diogomrts/vocetempo/enclosure/previews/panda_paws.png

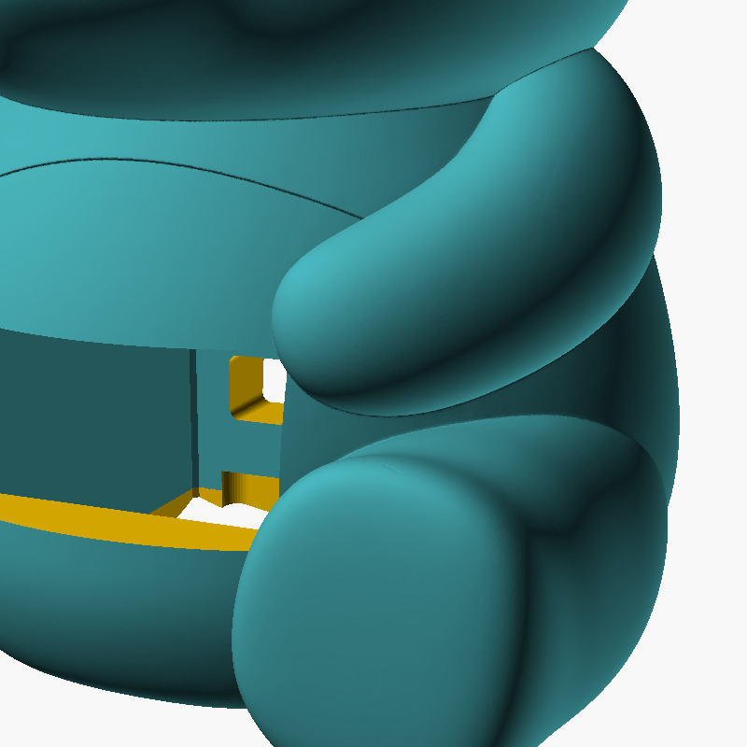
enclosure/previews/panda_paws.png
