diogomrts/vocetempo/enclosure/previews/cage_back.png

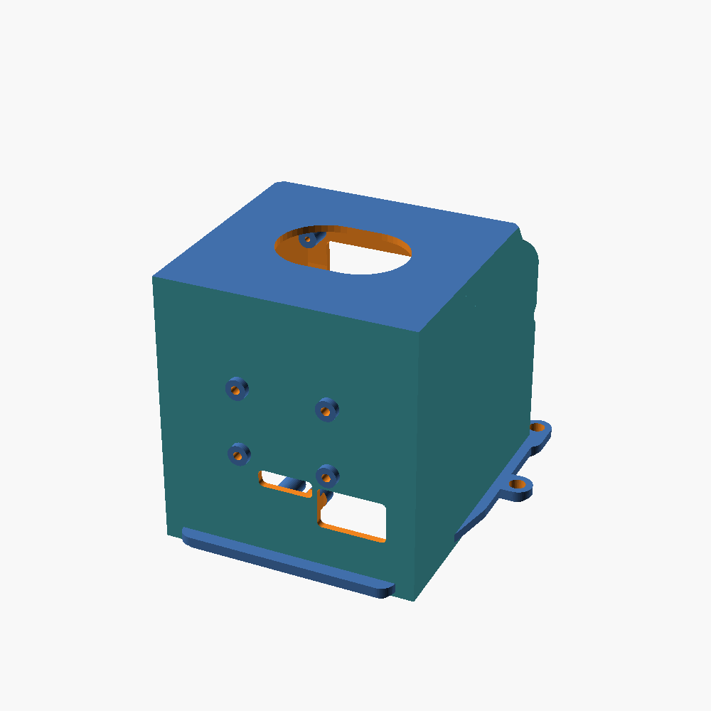
enclosure/previews/cage_back.png
