diogomrts/vocetempo/enclosure/previews/cage_cutouts_comparison_v8.png

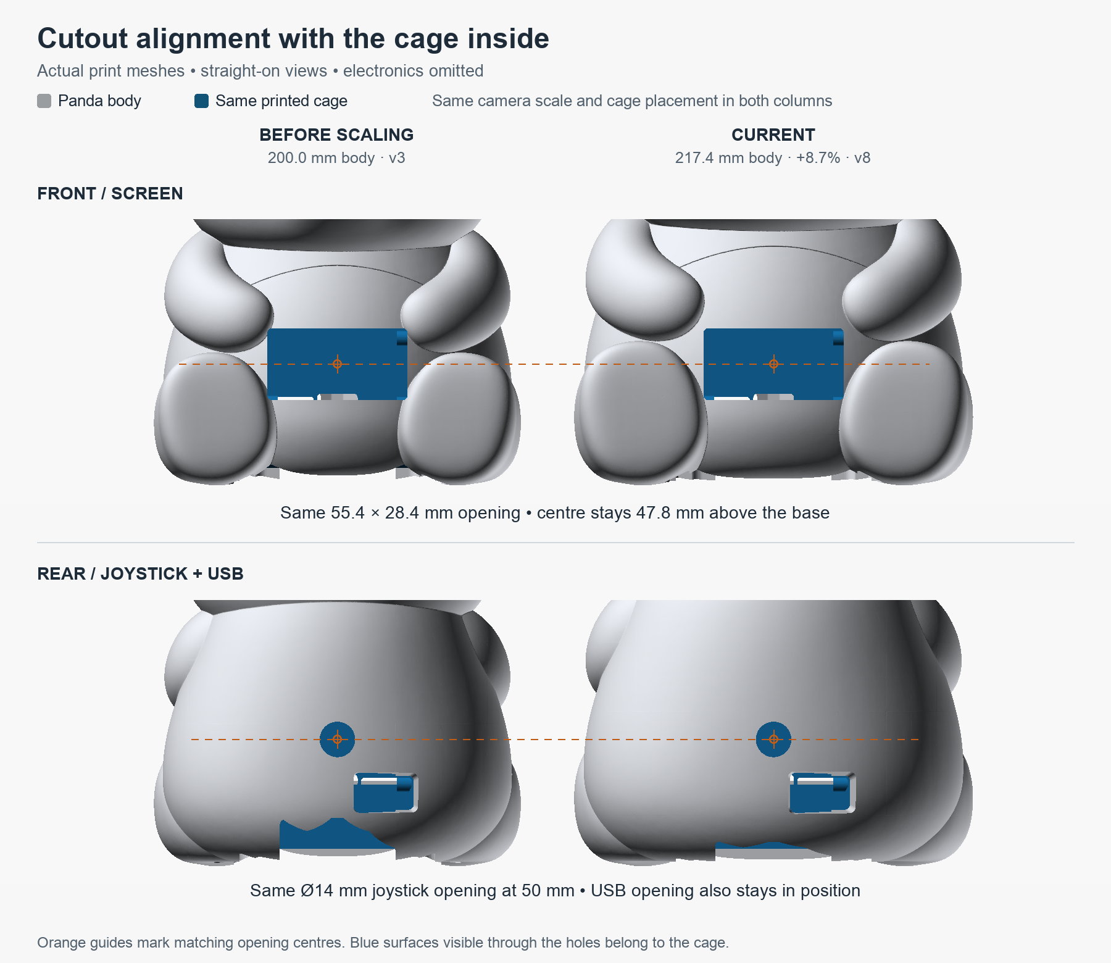
enclosure/previews/cage_cutouts_comparison_v8.png
