diogomrts/vocetempo/enclosure/previews/cage_final.png

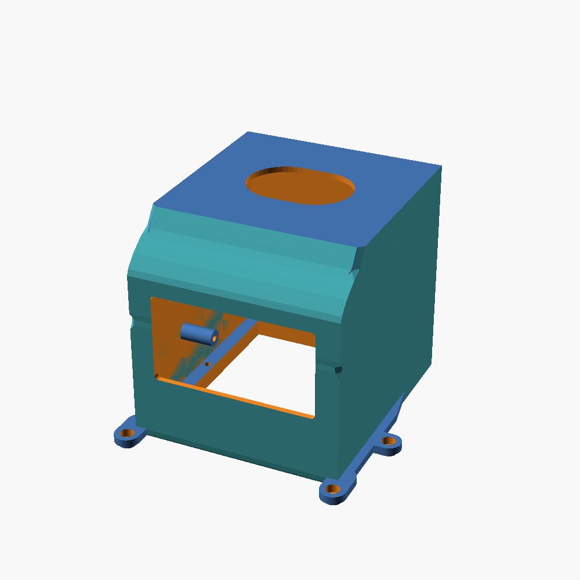
enclosure/previews/cage_final.png
