diogomrts/vocetempo/enclosure/previews/cage_section_comparison_v8.png

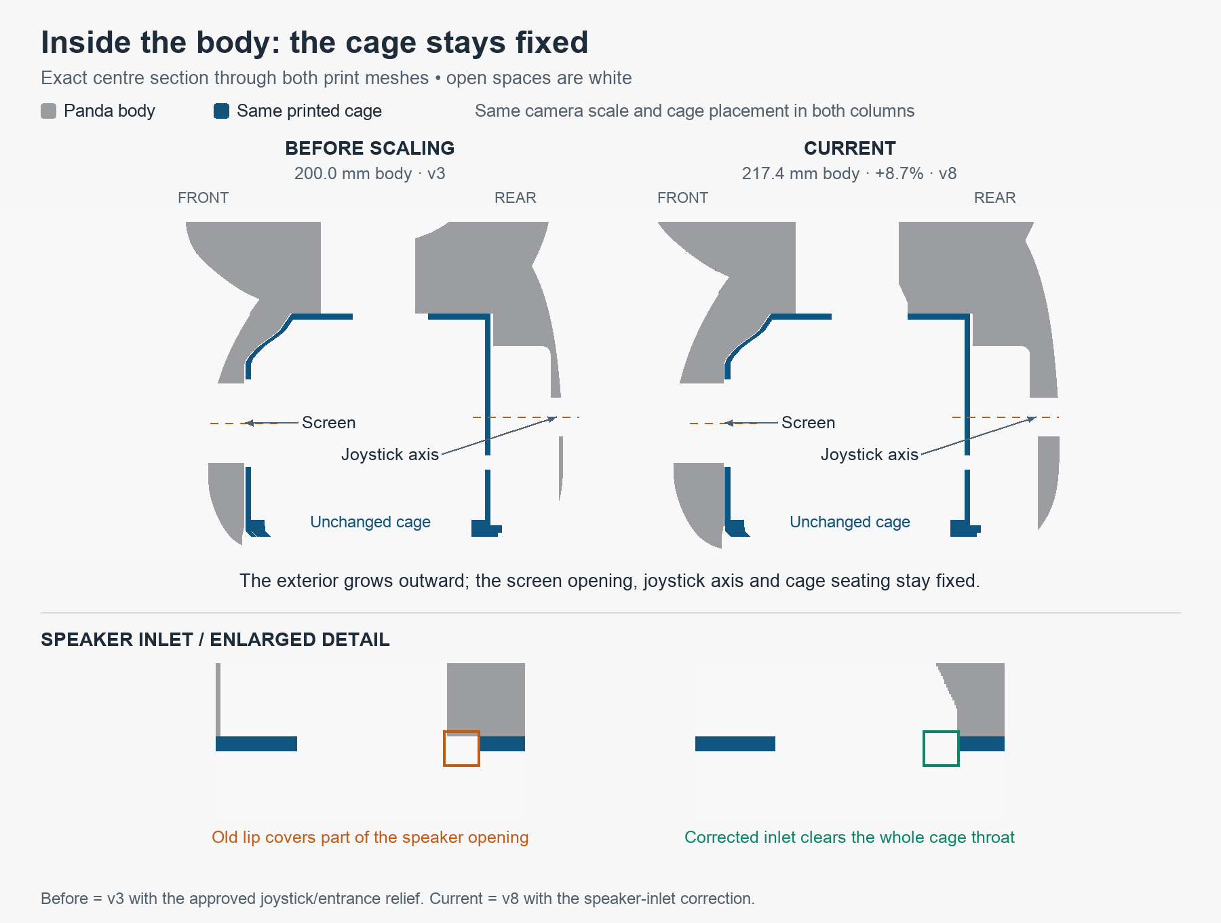
enclosure/previews/cage_section_comparison_v8.png
