diogomrts/vocetempo/enclosure/previews/cover.png

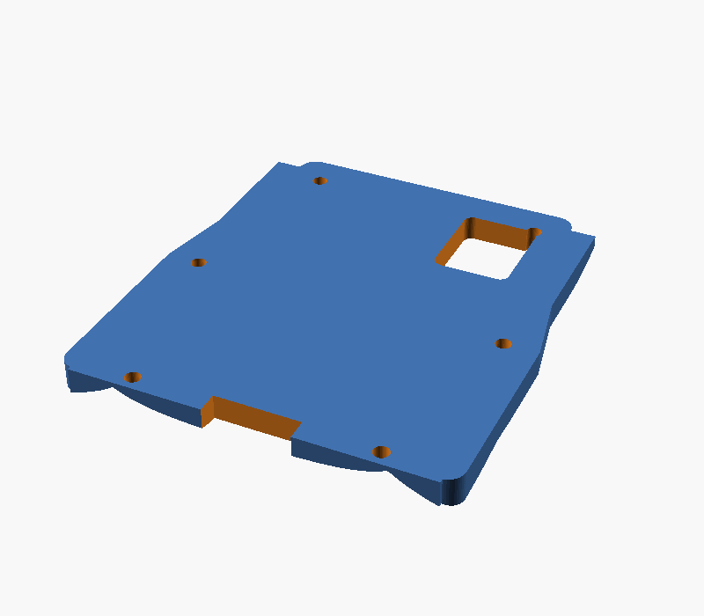
enclosure/previews/cover.png
