diogomrts/vocetempo/enclosure/previews/dfp_bar.png

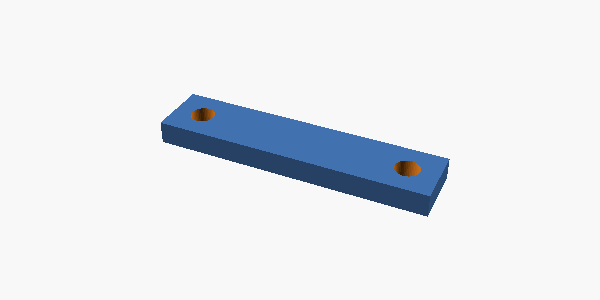
enclosure/previews/dfp_bar.png
