diogomrts/vocetempo/enclosure/previews/entrance_comparison_v3.png

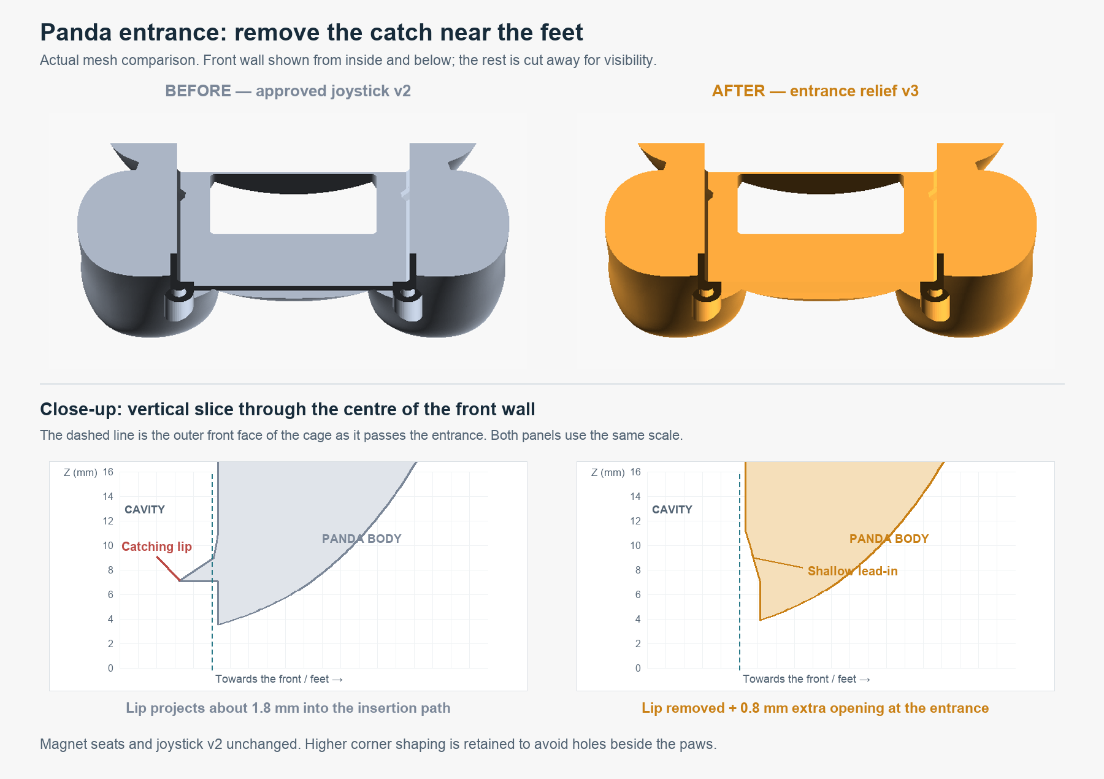
enclosure/previews/entrance_comparison_v3.png
