diogomrts/vocetempo/enclosure/previews/expanded_rump_comparison_v5.png

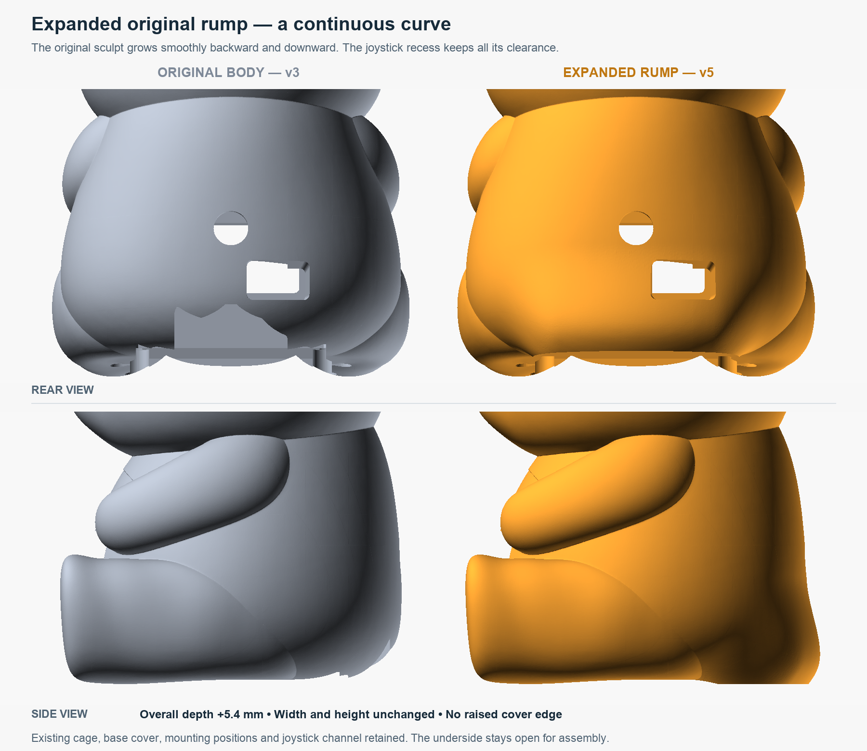
enclosure/previews/expanded_rump_comparison_v5.png
