diogomrts/vocetempo/enclosure/previews/fitcheck.png

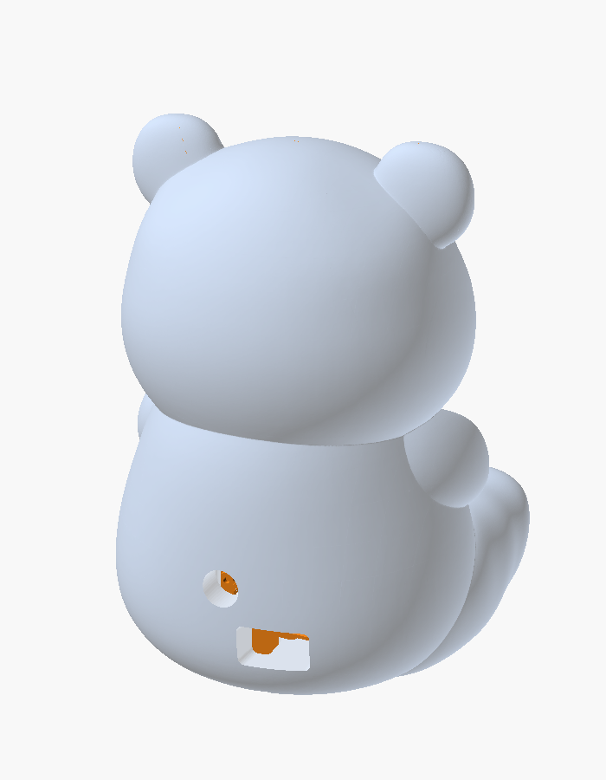
enclosure/previews/fitcheck.png
