diogomrts/vocetempo/enclosure/previews/fitcheck_section.png

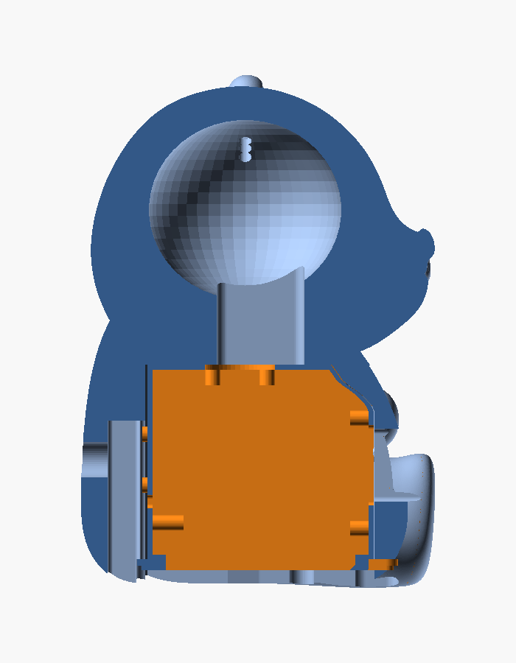
enclosure/previews/fitcheck_section.png
