diogomrts/vocetempo/enclosure/previews/joy_cap.png

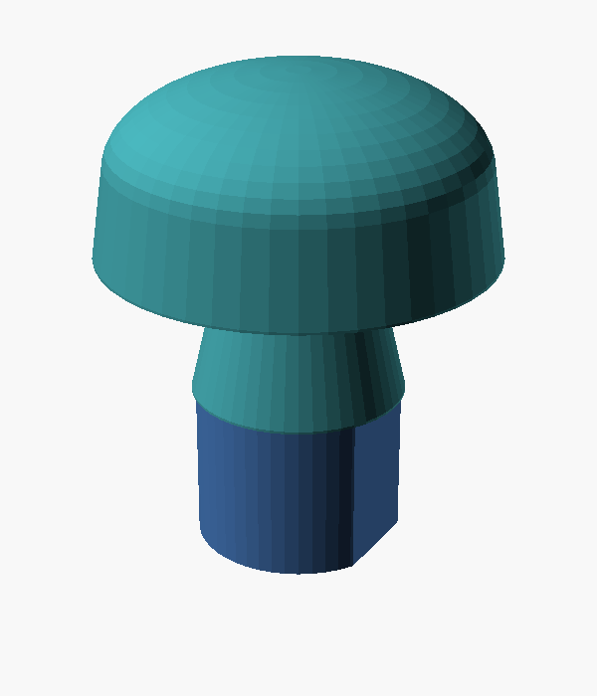
enclosure/previews/joy_cap.png
