diogomrts/vocetempo/enclosure/previews/joystick_bottom_comparison.png

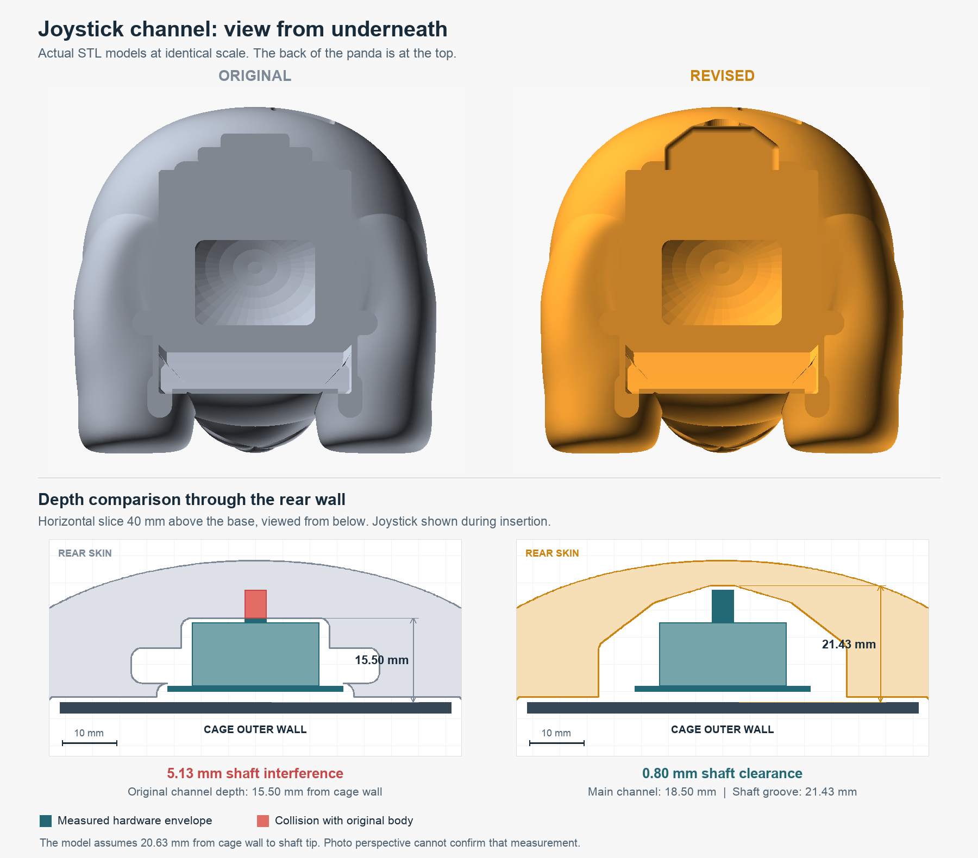
enclosure/previews/joystick_bottom_comparison.png
