diogomrts/vocetempo/enclosure/previews/joystick_bottom_comparison_v2.png

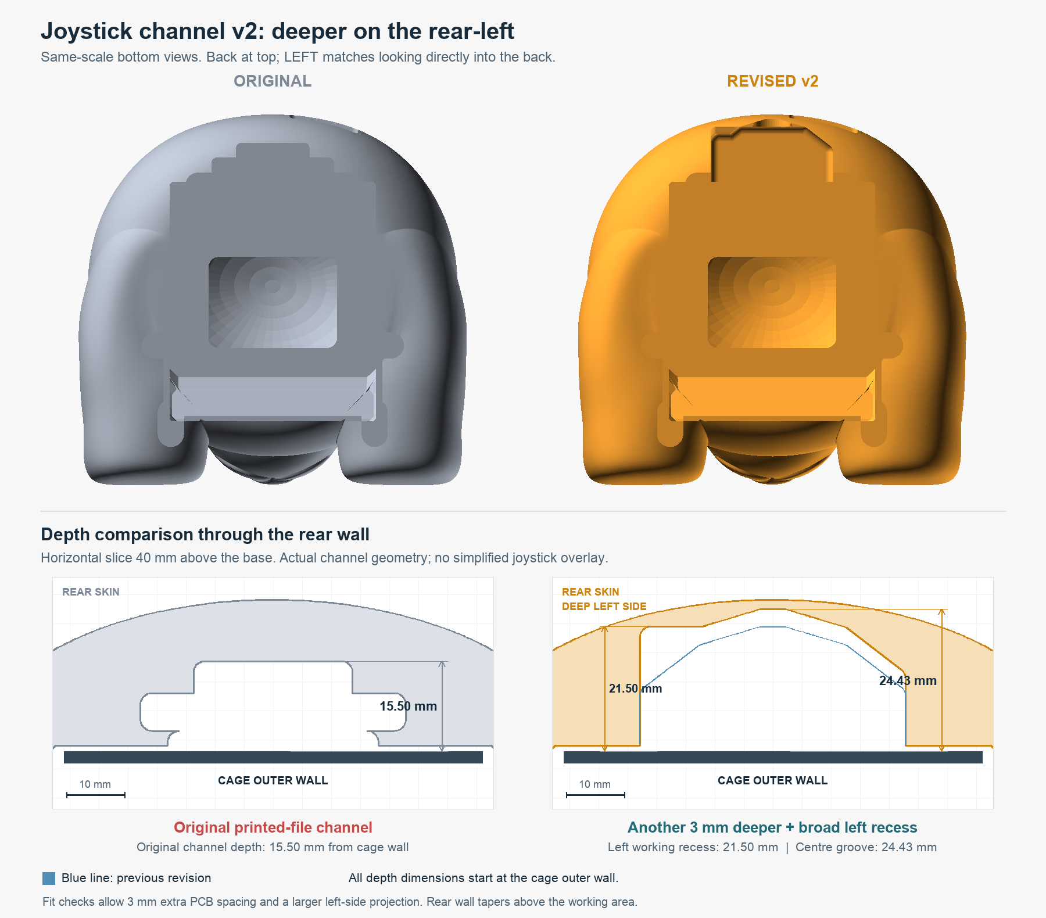
enclosure/previews/joystick_bottom_comparison_v2.png
