diogomrts/vocetempo/enclosure/previews/layout_walls.png

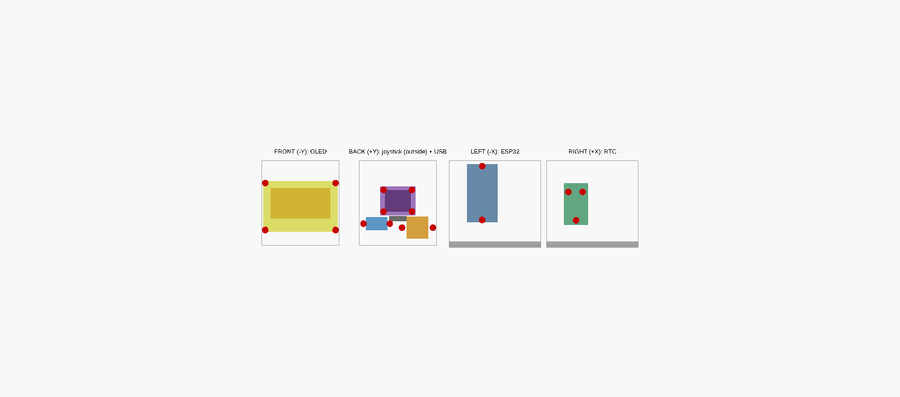
enclosure/previews/layout_walls.png
