diogomrts/vocetempo/enclosure/previews/panda_back.png

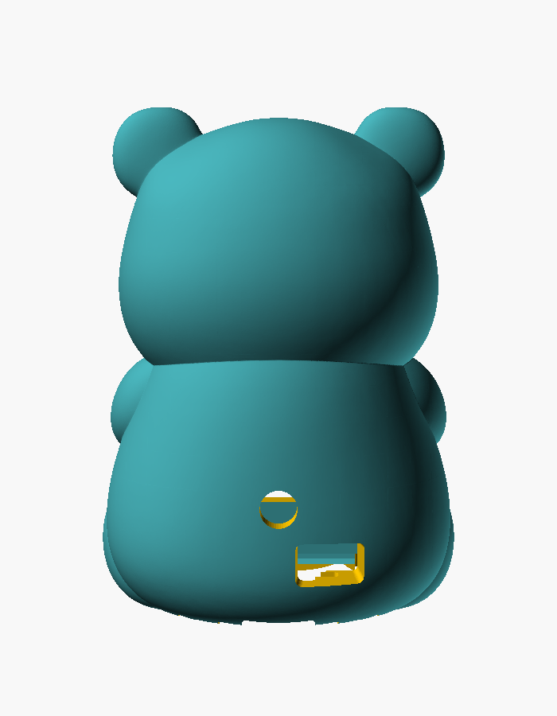
enclosure/previews/panda_back.png
