diogomrts/vocetempo/enclosure/previews/panda_body_v8_black_white.png

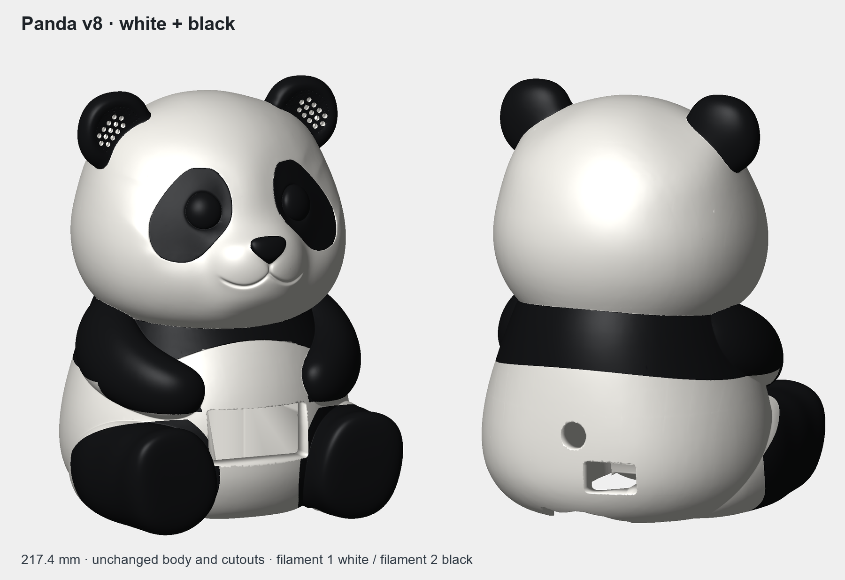
enclosure/previews/panda_body_v8_black_white.png
