diogomrts/vocetempo/enclosure/previews/panda_body_v8_black_white_bambu.png

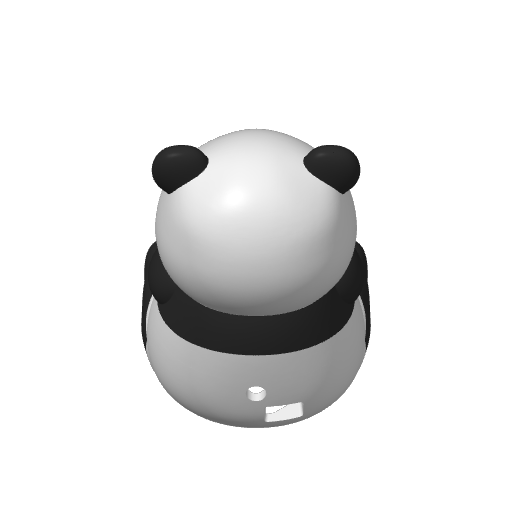
enclosure/previews/panda_body_v8_black_white_bambu.png
