diogomrts/vocetempo/enclosure/previews/panda_body_v8_paint_detail.png

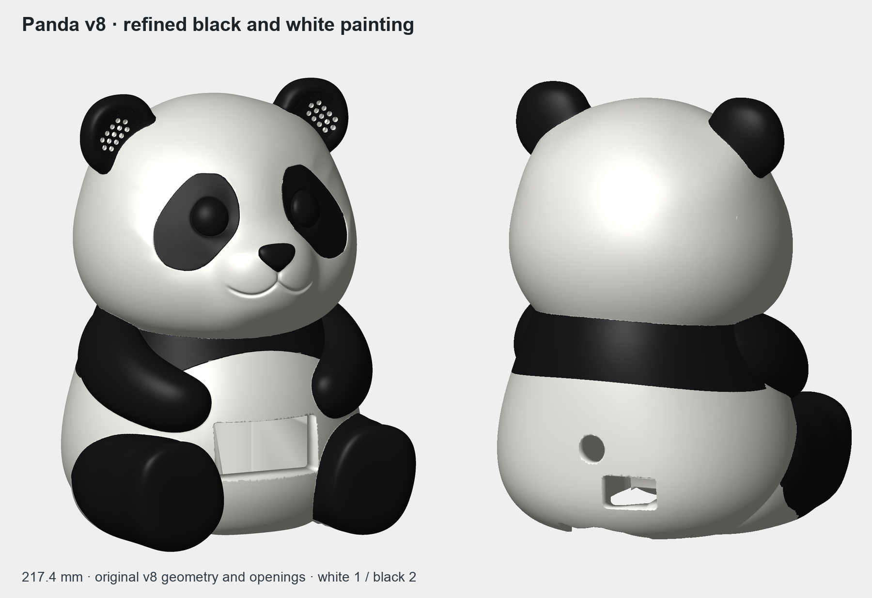
enclosure/previews/panda_body_v8_paint_detail.png
