diogomrts/vocetempo/enclosure/previews/panda_body_v8_paint_detail_closeups.png

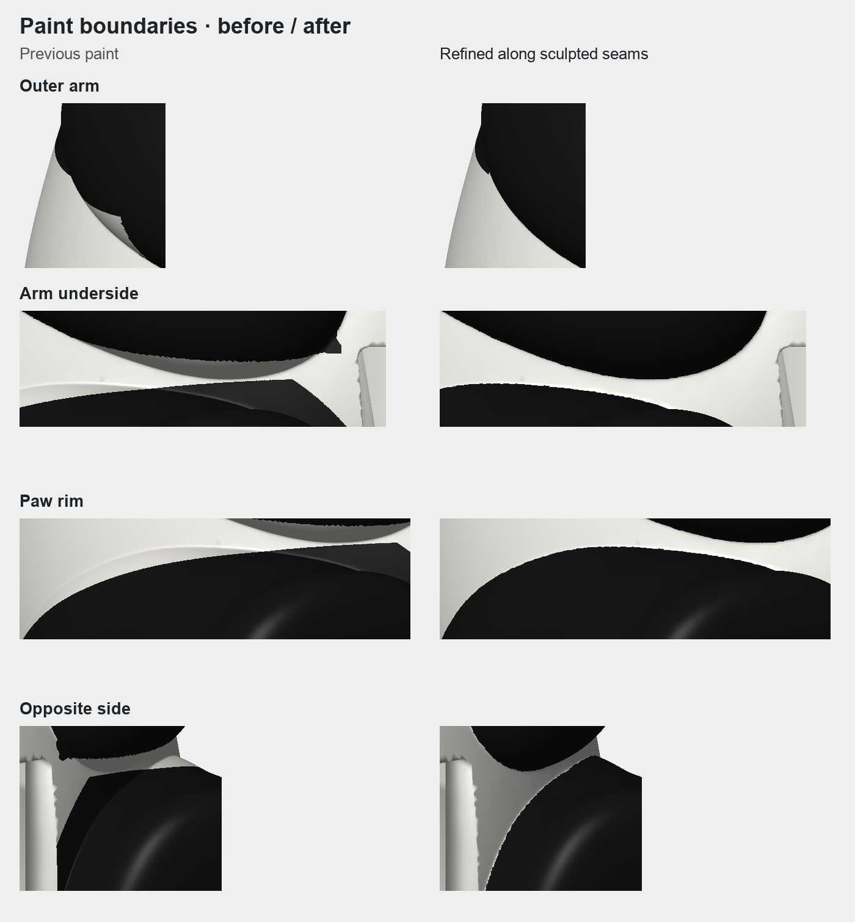
enclosure/previews/panda_body_v8_paint_detail_closeups.png
