diogomrts/vocetempo/enclosure/previews/panda_body_v8_paint_full_comparison.png

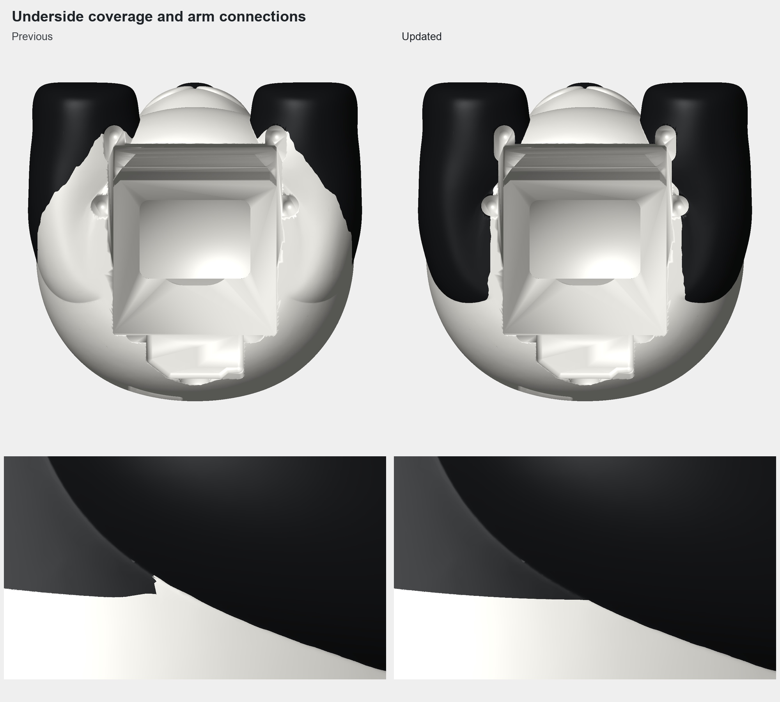
enclosure/previews/panda_body_v8_paint_full_comparison.png
