diogomrts/vocetempo/enclosure/previews/panda_body_v8_paint_full_turntable.gif

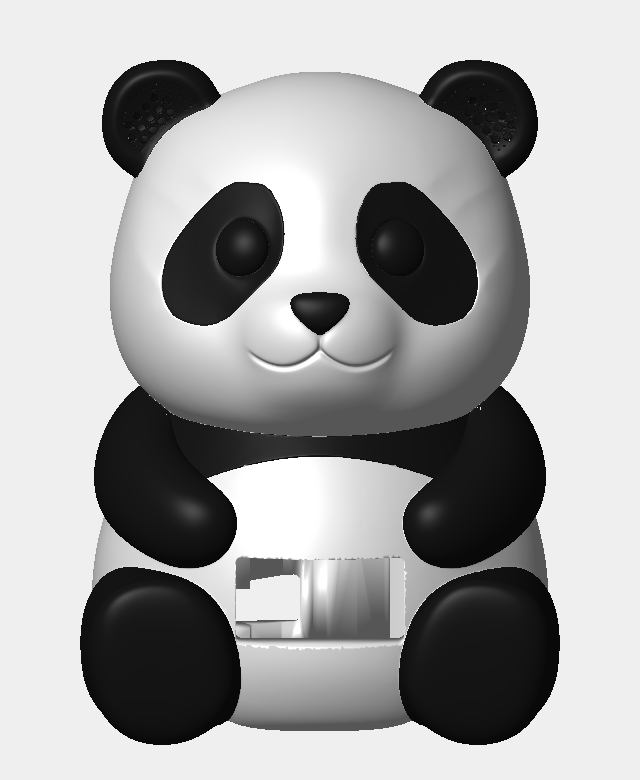
enclosure/previews/panda_body_v8_paint_full_turntable.gif
