diogomrts/vocetempo/enclosure/previews/panda_body_v8_paint_precision_closeups.png

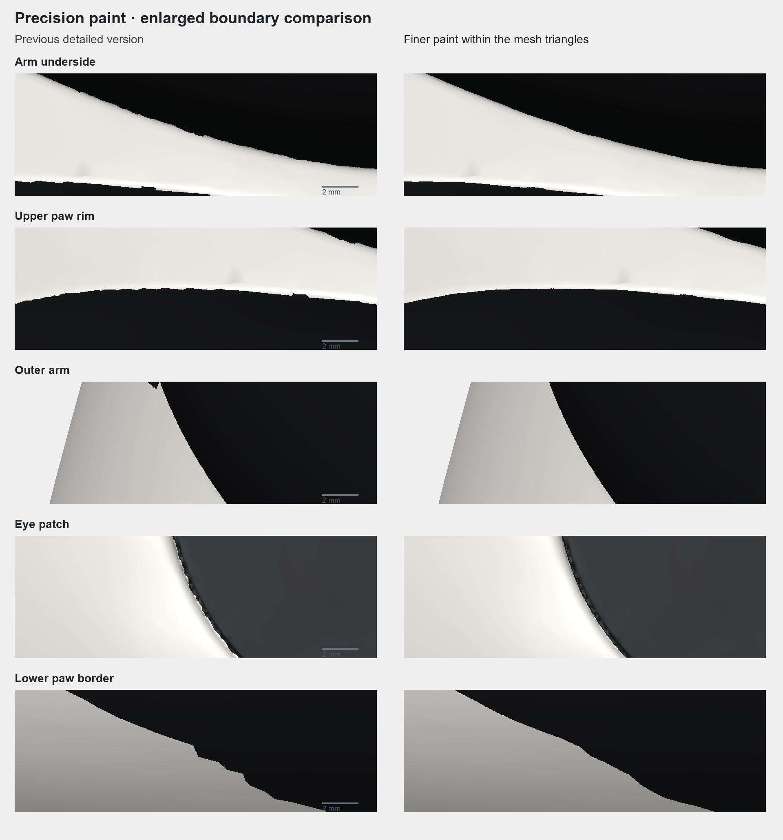
enclosure/previews/panda_body_v8_paint_precision_closeups.png
