diogomrts/vocetempo/enclosure/previews/panda_ear_grille.png

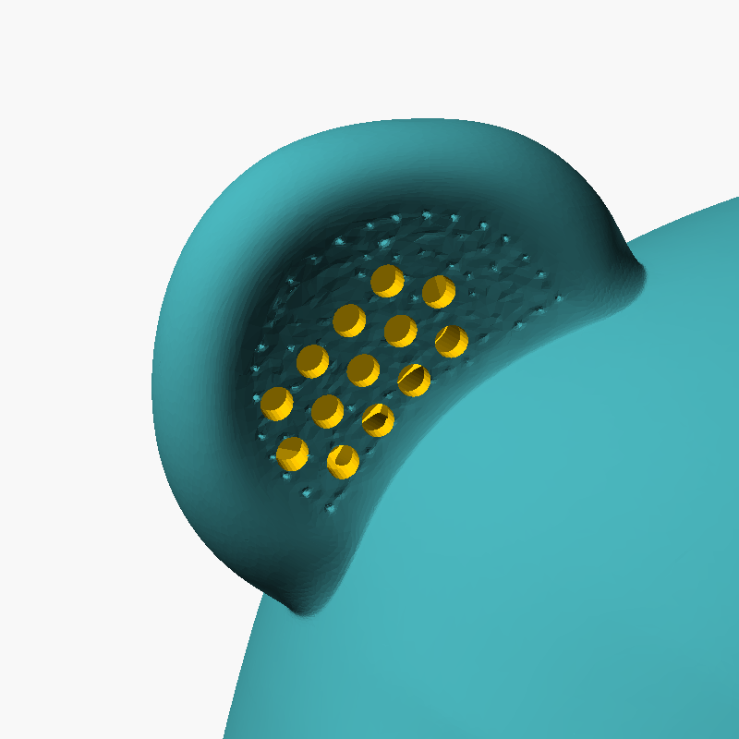
enclosure/previews/panda_ear_grille.png
