diogomrts/vocetempo/enclosure/previews/rear_cover_comparison_v4.png

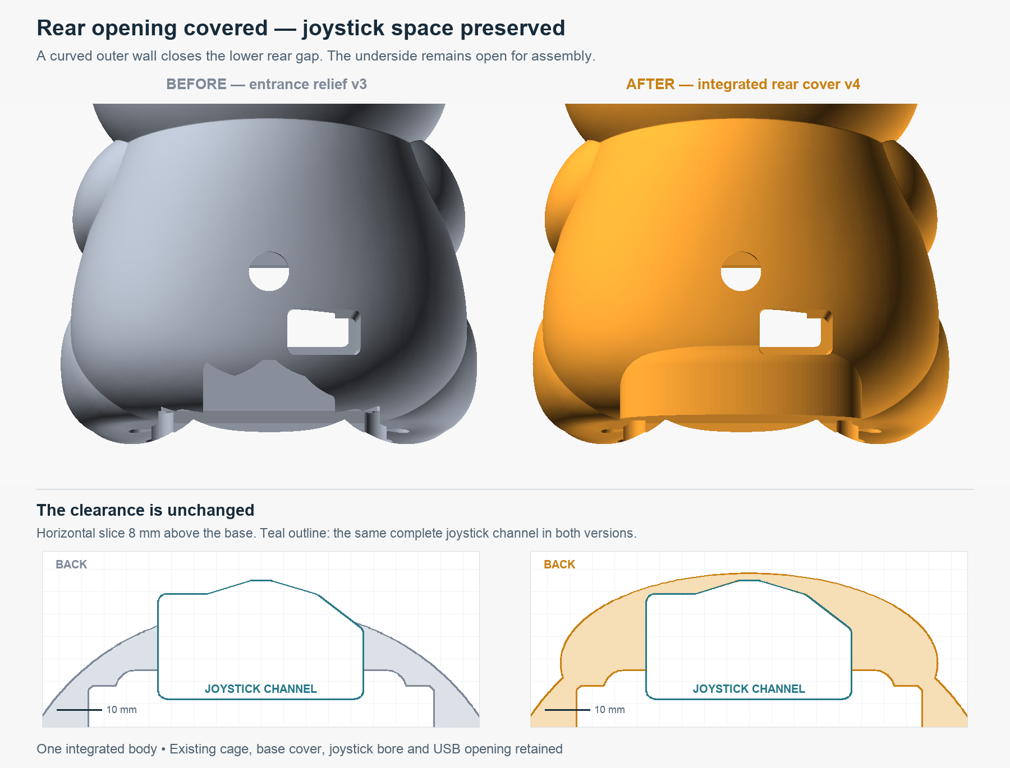
enclosure/previews/rear_cover_comparison_v4.png
