diogomrts/vocetempo/enclosure/previews/uniform_body_bottom_v6.png

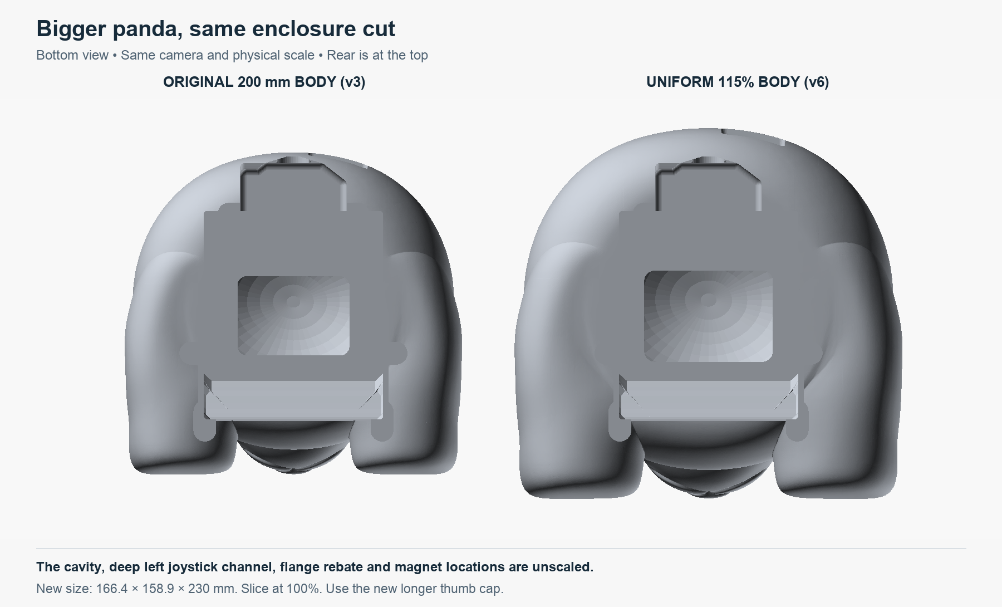
enclosure/previews/uniform_body_bottom_v6.png
