diogomrts/vocetempo/enclosure/previews/uniform_body_comparison_v7.png

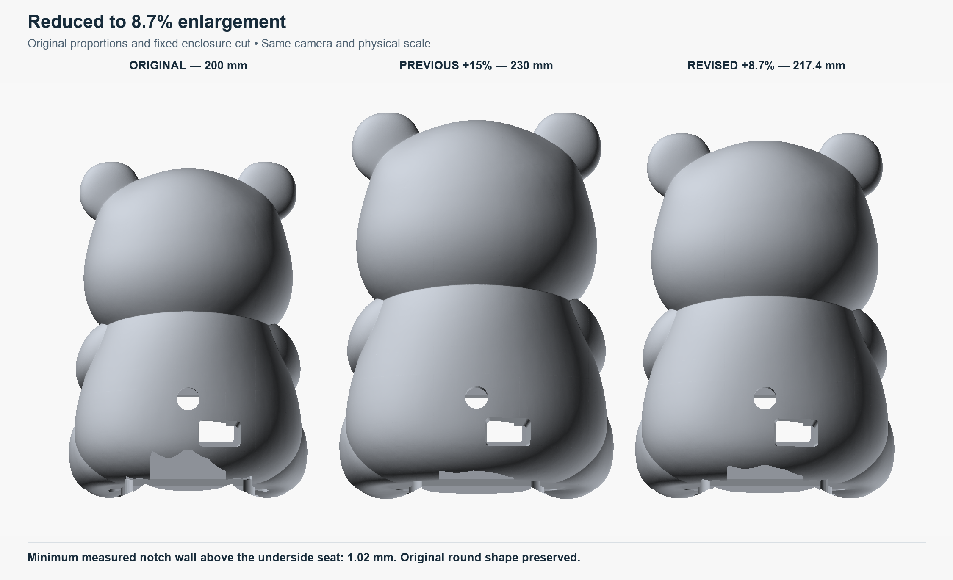
enclosure/previews/uniform_body_comparison_v7.png
