diogomrts/vocetempo/enclosure/previews/uniform_body_front_v6.png

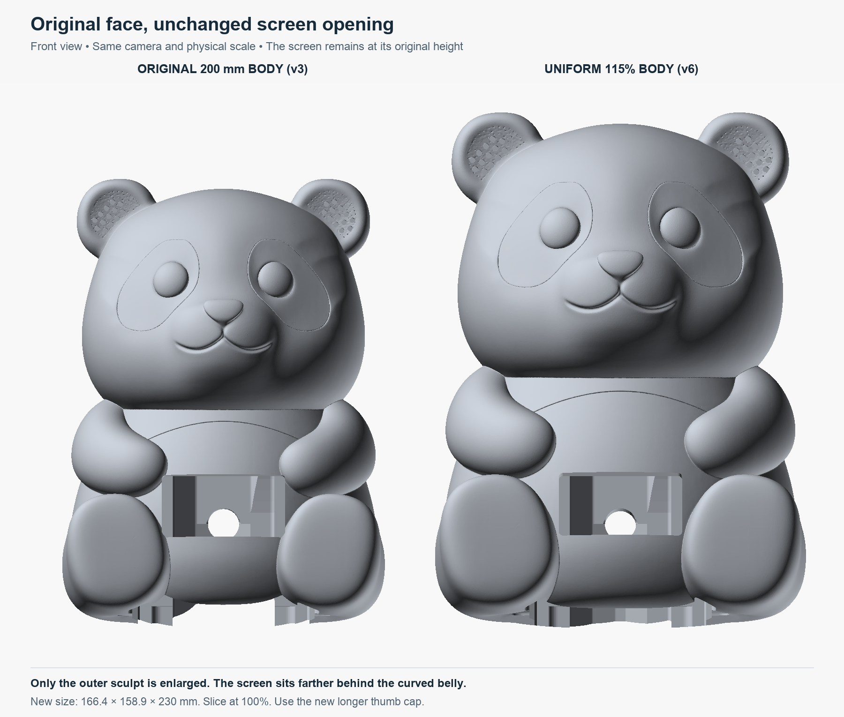
enclosure/previews/uniform_body_front_v6.png
