diogomrts/vocetempo/enclosure/previews/uniform_body_side_v6.png

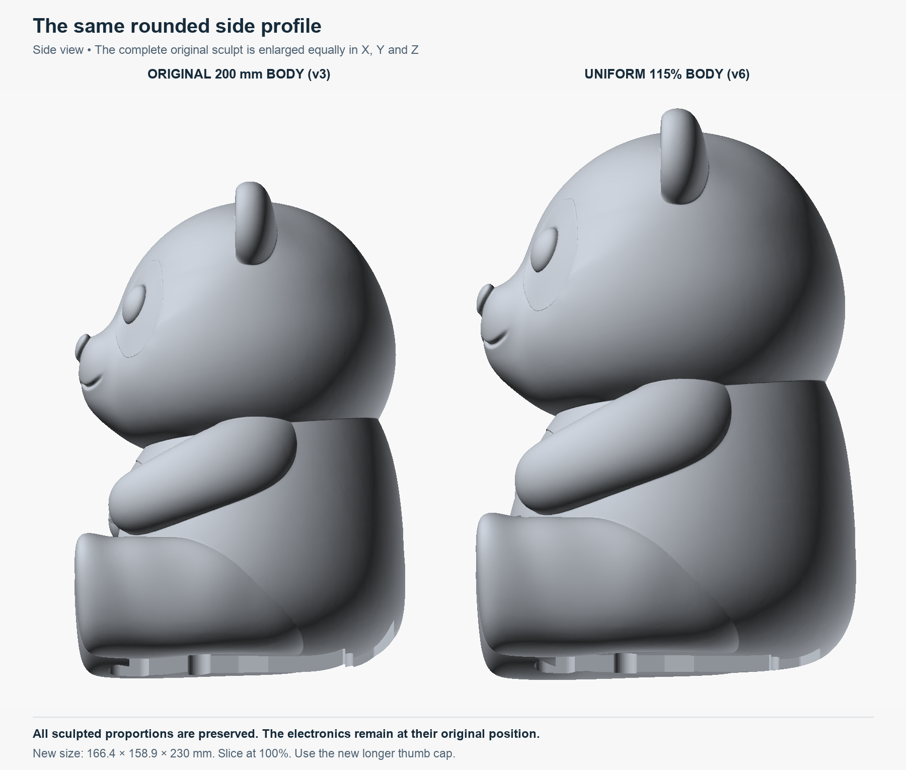
enclosure/previews/uniform_body_side_v6.png
